Camaraarthur/daemon/WORLD_DOMINATION_STRATEGY.md

# Daemon — World Domination Strategy
*April 5, 2026 — The Machiavelli Plan*

---

## The Category We Own

**"Device-native AI"** — AI that lives on YOUR devices, not someone else's data center.

Current "personal AI" = a chatbot that remembers your name. We redefine it:
- "Can you unplug your internet and still talk to your AI? If not, it's not yours."
- "Privacy you can verify with a multimeter."
- "One AI. All your devices."

---

## The Timing Play (CRITICAL)

Every breakout project rode a wave it didn't create. Our wave: **Apple WWDC June 2026.**

Apple will announce Siri 2.0 with multi-device AI agents. When they do, every tech journalist and developer will search for "open source alternative." If Daemon v0 is live, polished, and indexed BEFORE that announcement, we're the answer. "Open-source alternative to [hot paid thing]" is the most reliable viral pattern in developer tools.

**Target: v0 public and stable by late May 2026.**

Other waves to ride:
- EU AI Act high-risk obligations (August 2026) → "Daemon is compliant by design"
- Any major AI privacy scandal → "Privacy you can verify with a multimeter"
- Any Replika/Character.ai shutdown → "Your daemon can't be taken away"

---

## Phase 0: Before Launch (NOW → v0 public)

### IP Protection (do before ANYTHING goes public)
- [x] EUIPO SME Fund voucher submitted
- [ ] File Italian patent for privacy LED interlock (~€300)
- [ ] File "DAEMON" trademark at EUIPO when voucher approved (~€225 after reimbursement)
- [ ] CRITICAL: Patent must be filed BEFORE GitHub repo goes public

### Free Cloud Credits (15 min each)
- [ ] NVIDIA Inception
- [ ] Microsoft for Startups ($150K Azure)
- [ ] AWS Activate ($100-300K)

### Build the Ammo
- [ ] Film the multimeter video (60 sec, measure LED interlock pin)
- [ ] Record split-screen demo: ChatGPT vs Daemon (same prompt, Daemon knows you)
- [ ] Record "all devices connected" 30-sec clip (phone + laptop + RPi, one conversation)
- [ ] Prepare 3 blog posts (see Content Pipeline below)
- [ ] Print 500 stickers: "Privacy you can verify with a multimeter" + QR → daemon.page

### Community Infrastructure
- [ ] GitHub Discussions enabled (NOT Discord yet — 5 people in Discord is a ghost town)
- [ ] 15 "good first issue" labels with clear descriptions
- [ ] CONTRIBUTING.md that gets someone running in <5 minutes
- [ ] username.daemon.page working (every user = an ad)

---

## Phase 1: Launch Week (v0 goes public)

### Day 0: Show HN
- **Post:** `Show HN: Daemon – Open-source AI agent that connects all your devices`
- **Time:** Tuesday or Wednesday, 9 AM ET (2 PM CET)
- **Requirements:** Working demo anyone can try in <2 minutes, clean README, honest about limitations
- **Arthur camps in comments for 3+ hours answering everything**

### Day 0-1: Reddit Wave (staggered)
- **r/LocalLLaMA** (same day as HN, afternoon) — Frame: "I built a multi-device AI agent with BYOK. Supports local models."
- **r/selfhosted** (Day 1) — Frame: "Self-hosted AI agent with zero cloud dependency. Your data stays on your devices."
- **r/SideProject** (Day 2) — Frame: build story, solo founder, Turin, Arduino heritage

### Day 0: Newsletter Submissions
Submit to all simultaneously:
- Console.dev (PERFECT fit — they review CLI tools)
- TLDR AI
- The Rundown AI
- Changelog News
- AlphaSignal
- Ben's Bites (email directly)

### Day 1-3: Twitter/X
- Post the multimeter video
- Post the split-screen demo
- Tag/quote-tweet relevant accounts (see Target List)
- Start the build-in-public thread

### Day 3-7: YouTube Outreach
DM these creators with a concise pitch (3 sentences + demo link + GitHub):
- **Cole Medin** — Reviews smaller AI agent tools specifically
- **Matthew Berman** — Reviews AI tools, responsive to DMs
- **Dreams of Code** — CLI tool focused
- **All About AI** — Hands-on demos of smaller projects
- **NetworkChuck** — Self-hosted angle

### Day 7: Podcast Pitches
- devtools.fm (specifically about developer tools)
- Changelog / The Changelog (THE open-source podcast)
- Latent Space (DM swyx on Twitter)
- Software Engineering Daily
- Indie Hackers Podcast

---

## Phase 2: First 100 Users (Weeks 2-6)

### Turin IRL — "Collison Installation"
Get 10 loyal users by physically installing Daemon on their devices:

1. **Talk at Politecnico di Torino** — Contact DAUIN department, offer guest lecture on "Multi-device AI agents." Bring the PCB. Let students hold it.
2. **Toolbox Coworking lightning talk** — 15-min demo, split-screen, let people try it live
3. **Weekly "Daemon Office Hours"** — Thursday 6PM, Toolbox or a coffee shop. "Bring your laptop, I'll set up your daemon." This is the Stripe "Collison Installation" playbook.
4. **Arduino community crossover** — Post in Arduino forums. "Built in Turin, where Arduino was born."
5. **GDG Torino / Linux Day** — Open-source + AI talk

### Sticker Campaign
- 500 stickers, two designs: (a) Daemon logo, (b) "My AI runs locally" + QR code
- Distribute at: Toolbox, Politecnico library, TAG, coffee shops near university
- Cost: ~€40. Impact: laptops → conferences → years of impressions

### Content Pipeline (weekly)
| Week | Content | Platform |
|---|---|---|
| 1 | "I designed a 160-component PCB to make AI trustworthy" | HN, blog |
| 2 | KiCad PCB layout time-lapse | Twitter/X, YouTube |
| 3 | "The LED that can't lie" — privacy interlock deep dive | HN, blog |
| 4 | "My first 3 PCB designs failed" — failure content | Twitter/X, Reddit |
| 5 | BOM breakdown — every component and its cost | Reddit r/electronics, blog |
| 6 | "What happens when the internet goes down" — offline test video | Twitter/X, YouTube |

### Engage (don't promote) in These Communities
- **Latent Space Discord** — swyx's community, AI engineers
- **LocalLLaMA Discord** — Local AI enthusiasts
- **Ollama Discord** — BYOK angle
- **Anthropic Discord** — Claude users
- Spend 2 weeks being helpful BEFORE mentioning Daemon

---

## Phase 3: 100 → 1,000 Users (Months 2-4)

### Viral Mechanics (built into the product)
- **username.daemon.page** — Every deploy is an ad (Vercel model)
- **"Daemon Connected" status cards** — Shareable: "3 devices, 47 days uptime, 100% local"
- **Daemon fingerprint** — Unique visual per instance (like GitHub identicons). People screenshot and share.
- **CLI easter egg** — 1 in 50 commands: "Enjoying Daemon? ⭐ github.com/..."
- **"Works with Daemon" badge** — Other projects put it in their README
- **Referral unlock** — "Invite 3 friends, unlock multi-model routing"

### Content Creators (Tier 2 — after traction)
Reach out when you have 500+ stars:
- **Fireship** — Watches HN/Twitter trends, will find you if you trend
- **Theo (t3.gg)** — Very opinionated, covers indie tools
- **The Primeagen** — Reacts to trending dev content
- **sentdex** — Python/AI, covers open-source

### Press Outreach
When you have 1,000+ stars and a working hardware prototype:

| Publication | Angle |
|---|---|
| **Hackaday** | The PCB, the LED interlock, the build. tips@hackaday.com |
| **Ars Technica** | Privacy architecture, local-first AI |
| **The Verge** | "This guy built his own Apple Intelligence" |
| **Wired Italy** | Turin founder, Arduino heritage, Italian innovation |
| **404 Media** | Hardware privacy verification, surveillance resistance |
| **The Register** | "Bloke in Turin builds AI pendant with a soldering iron" |
| **Tom's Hardware** | The pendant, the PCB design |
| **Il Sole 24 Ore / Nova** | Italian startup, local success story |

**Pitch template (3 sentences):**
> "I'm building Daemon, an open-source AI that runs on your own devices with a custom 160-component hardware pendant. Unlike cloud AI, the microphone has a hardware interlock you can verify with a multimeter — no software can override it. Launching [date], want an early look? [link]"

---

## Phase 4: Kickstarter (Months 4-6)

### Prerequisites
- [ ] 2,500+ email signups (20-40% convert to backers)
- [ ] Working hardware prototype (not just renders)
- [ ] Professional renders + real photos (need both)
- [ ] 2-3 minute video: Problem (30s) → Demo (60s) → Why you (30s) → Ask (15s)
- [ ] 500+ GitHub stars as social proof

### Launch Strategy
- Set funding goal LOW (need €50K? Set goal at €15K → "funded in 48 hours" story)
- Early backer reward: username.daemon.page (viral mechanic as reward)
- Stretch goals planned in advance (each = news hook + excuse to email list)
- Pre-launch page on Kickstarter 7 days before (followers get notified)

### Kickstarter Narrative
- "Your daemon already exists as software. Now give it a body."
- "Built in Turin, where Arduino was born. Open source down to the circuit board."
- "The AI device with privacy you can measure, not just promise."

---

## Phase 5: Amazon Store + Ecosystem (Month 3+)

### "Daemon-Compatible Devices" Page
Create a page on daemon.page with affiliate links:
- Single-board computers (Raspberry Pi 5, Orange Pi)
- USB microphones, cameras, sensors
- Smart home bridges (Zigbee/Z-Wave USB dongles)
- Storage for local AI models
- Networking (Tailscale-compatible hardware)
- "Daemon Starter Kit" — curated everything-you-need list

### Revenue: Primarily Marketing
~€75/month in affiliate revenue, but the real value:
- Makes Daemon feel like a platform/ecosystem
- Content hooks ("I tested 5 USB mics for local AI — here's the best")
- Traffic from Amazon search → daemon.page

---

## Target People (The Hit List)

### Twitter/X — The Kingmakers
| Handle | Who | Why |
|---|---|---|
| @simonw | Simon Willison | #1 target. CLI tools, open source, AI, privacy, SQLite. If he blogs about you, you're legitimized. |
| @levelsio | Pieter Levels | Indie hacker godfather. Loves solo founders building in public. |
| @swyx | Shawn Wang | "AI Engineer" movement. Runs AI Engineer Summit. |
| @karpathy | Andrej Karpathy | Seismic when he covers tools (rare). |

### YouTube — Drive GitHub Stars
| Creator | Subs | Why |
|---|---|---|
| Cole Medin | 100K+ | Reviews smaller AI agent tools, very accessible |
| Matthew Berman | 400K | AI tool reviews, responsive to DMs |
| Dreams of Code | 200K | CLI/terminal tool focused |
| NetworkChuck | 4M | Self-hosted, CLI, AI |
| Jeff Geerling | 1M+ | Hardware + self-hosted. Perfect for hardware phase. |

### Podcasts
| Show | Access |
|---|---|
| devtools.fm | DM on Twitter |
| The Changelog | Submit via changelog.com |
| Latent Space | DM swyx |
| Indie Hackers | Apply on site |

---

## The Turin Advantage

**Arduino was born in Turin.** Use this:
- "Daemon is built in Turin, where Arduino was born. Hardware-first open source is in our DNA."
- Politecnico di Torino = recruiting ground (34K students, strong CS/EE)
- I3P incubator = instant credibility
- Toolbox Coworking = home base + events
- CIM4.0 (Turin EDIH) = free AI services for Piemonte SMEs

---

## Budget

| Item | Cost | When |
|---|---|---|
| 500 stickers | €40 | Now |
| Italian patent filing | €300 (€100 after SME Fund) | This month |
| DAEMON trademark | €900 (€225 after SME Fund) | When voucher approved |
| Domain/hosting | €50-200/month | Already running |
| Everything else | €0 | Sweat equity |

**Total cash needed to launch: ~€500**

Everything else is time, creativity, and relentless execution.

---

## The One Rule

**Ship, then optimize.** The product must work flawlessly for 10 people before marketing to 10,000. Every bug a creator encounters on camera is a permanent scar. Every delightful first experience is a permanent evangelist.

The strategy is:
1. Get 10 local users who love it
2. Film them using it
3. Use that footage to get 100
4. Use those 100 to get 1,000
5. Use those 1,000 for Kickstarter
6. Use Kickstarter for press
7. Use press for scale

No step can be skipped. No step is optional.
