Camaraarthur/daemon/docs/positioning.md

# Daemon — Positioning v1

> **Status:** locked.
> **Date:** 2026-04-08
> **Pair with:** vision.md (the WHAT). This doc is the PITCH.

## 1. The wedge — sharper than before

### v1 audience: Claude Code power users (developers)

**Why this audience first:**
- Highest acute pain (already daily users hitting "my agent died when I closed my laptop")
- Lowest CAC: ~5 places to reach them (Anthropic Discord, /r/ClaudeAI, HN, /r/LocalLLaMA, a few Twitter circles)
- Strongest demos (devs film themselves; dev demos go viral)
- They overlap with privacy-conscious people, homelabbers, hardware tinkerers — picking devs gets the others for free
- AGPLv3 actually matters here (only audience that reads licenses)
- Reference customers ARE the artifact (a daemon-built workflow on GitHub is worth 10× a testimonial)

**Why NOT the casual prosumer first:**
- They expect a website, not a daemon process
- They need a trust brand we don't have yet
- Conversion path needs polished onboarding + hand-holding
- Won't pay until they see other people happy first

**Why NOT homelab first either:**
- They want fun, not relief
- Lower density than Claude Code communities
- They overlap with devs anyway — devs is a strict superset

### v1.5 audience: privacy-first knowledge workers + homelabbers

Natural extension of v1. Privacy is the closer for v1 devs, the opener for v1.5 audiences.

### v2 audience: casual prosumers

After the wedge produces organic word of mouth.

## 2. The two seductions

The dev pitch and the casual pitch are *different surfaces of the same product*. They share the same install, same protocol, same architecture — but the framing is different.

### Dev seduction (v1 — lead with this)

> Your Claude Code, on every device you own.

You already live in Claude Code. But your agent dies when you close the lid, forgets when you switch machines, and can't touch your phone. Daemon gives Claude Code a persistent memory, a web UI, and a tool bus that reaches every device you own — laptop, desktop, phone, daemon-key — as one continuous session. Bring your own Anthropic key. Your data never touches our servers.

### Casual seduction (v1.5)

> An AI that searches your computer, runs in the background, and pings you when it's done.

Drop the pendant on your desk. Pair it with your phone. Now an AI agent runs while you sleep — checks your email, watches your sensors, runs jobs, builds you tools. Ask it from your phone to find that file you saved last Tuesday. It does. No upload, no chat-bot UI for the simple stuff. Just a thing that works on your real life.

The bridge between them: the vibe coder's primitive set is the same. The dev uses it to build personal automations on top of their existing Claude Code workflow. The casual user gets pre-built primitives (morning briefing, find-my-file, build-me-a-tool) that come out of the box.

## 3. The "so what" — locked

**One sentence:**
> Daemon is the AI agent that runs on your stuff, not in someone's cloud.

**Hero paragraph:**
> Daemon runs a small agent on every device you own — laptop, desktop, phone, the always-on box on your desk. They join one continuous AI agent that has access to your files, your sensors, your shell, your screen. Your conversations and memory live on those devices, never on our servers. Bring your own model API key. Open source, self-hostable, AGPLv3. The same agent, the same memory, on everything you actually use.

**30-second verbal pitch (memorize, end with URL not a question):**
> "You know Claude Code — the terminal thing? I use it every day but it dies when I close my laptop and it can't touch my phone. So I built daemon — same agent, same memory, but it runs as a tiny process on every device I own. I can ask it from my phone to grep a file on my desktop and it just does it. My data never hits a server, the relay only routes messages. Open source, works with any model. It's at daemon.page."

**The pitch is true.** Anchored in the actual technology (per-device daemon, persistent memory, BYOK relay). Legible to a non-technical person ("ask my phone to do something on my laptop"). Picks a category — "Claude Code" — that everyone in the wedge already knows. **Cursor won by being "VSCode + AI." Daemon wins by being "Claude Code + multi-device."**

## 4. Strategic NO list (don't say these in v1)

- **Don't lead with "AI agent."** Crowded category, you lose on polish.
- **Don't lead with "privacy" or "AGPLv3."** Privacy is the closer, not the opener. Signals "not for serious work" to devs even though it's true.
- **Don't mention the daemon-key Pi.** Sounds like a Kickstarter, not a product. Park it.
- **Don't say "personal AI."** Rabbit / Humane / Friend poisoned that brand.
- **Don't say "memory for agents."** That's Letta's lane and it describes mechanism, not pain.
- **Don't show a chat window as the primary screenshot.** Show "phone running command on laptop." That's the unique demo.
- **Don't compete on model quality.** BYOK = model-agnostic, don't get drawn into "smarter than GPT-5."
- **Don't use the word "daemon" in the tagline without context.** Half the audience hears the technical term, the other half hears the demon.
- **Don't sell to enterprises in v1.** Long sales cycles, kills the flywheel.
- **Don't add Telegram integration in v1.** Notifications are owned natively.
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
