Camaraarthur/daemon/test-results/20260405-204737/after_delay.png

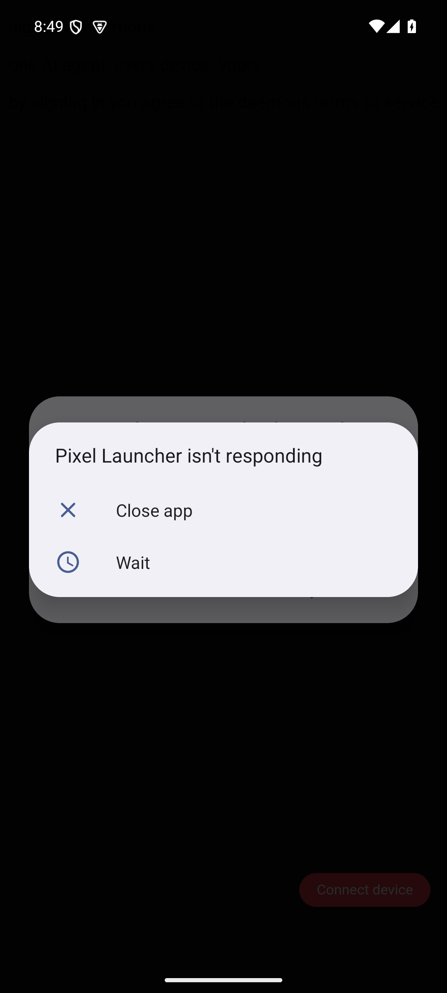
test-results/20260405-204737/after_delay.png
