Camaraarthur/daemon/server/esp32_firmware/font5x7.py

# 5x7 bitmap font for MicroPython ST7789 display
# Each character is 5 columns of 7-bit rows, packed as bytes
# Covers ASCII 32-126

FONT = {
    32: b'\x00\x00\x00\x00\x00',  # space
    33: b'\x00\x00\x5f\x00\x00',  # !
    34: b'\x00\x07\x00\x07\x00',  # "
    39: b'\x00\x00\x07\x00\x00',  # '
    40: b'\x00\x1c\x22\x41\x00',  # (
    41: b'\x00\x41\x22\x1c\x00',  # )
    42: b'\x14\x08\x3e\x08\x14',  # *
    43: b'\x08\x08\x3e\x08\x08',  # +
    44: b'\x00\x50\x30\x00\x00',  # ,
    45: b'\x08\x08\x08\x08\x08',  # -
    46: b'\x00\x60\x60\x00\x00',  # .
    47: b'\x20\x10\x08\x04\x02',  # /
    48: b'\x3e\x51\x49\x45\x3e',  # 0
    49: b'\x00\x42\x7f\x40\x00',  # 1
    50: b'\x42\x61\x51\x49\x46',  # 2
    51: b'\x21\x41\x45\x4b\x31',  # 3
    52: b'\x18\x14\x12\x7f\x10',  # 4
    53: b'\x27\x45\x45\x45\x39',  # 5
    54: b'\x3c\x4a\x49\x49\x30',  # 6
    55: b'\x01\x71\x09\x05\x03',  # 7
    56: b'\x36\x49\x49\x49\x36',  # 8
    57: b'\x06\x49\x49\x29\x1e',  # 9
    58: b'\x00\x36\x36\x00\x00',  # :
    63: b'\x02\x01\x51\x09\x06',  # ?
    65: b'\x7e\x11\x11\x11\x7e',  # A
    66: b'\x7f\x49\x49\x49\x36',  # B
    67: b'\x3e\x41\x41\x41\x22',  # C
    68: b'\x7f\x41\x41\x22\x1c',  # D
    69: b'\x7f\x49\x49\x49\x41',  # E
    70: b'\x7f\x09\x09\x09\x01',  # F
    71: b'\x3e\x41\x49\x49\x7a',  # G
    72: b'\x7f\x08\x08\x08\x7f',  # H
    73: b'\x00\x41\x7f\x41\x00',  # I
    74: b'\x20\x40\x41\x3f\x01',  # J
    75: b'\x7f\x08\x14\x22\x41',  # K
    76: b'\x7f\x40\x40\x40\x40',  # L
    77: b'\x7f\x02\x0c\x02\x7f',  # M
    78: b'\x7f\x04\x08\x10\x7f',  # N
    79: b'\x3e\x41\x41\x41\x3e',  # O
    80: b'\x7f\x09\x09\x09\x06',  # P
    81: b'\x3e\x41\x51\x21\x5e',  # Q
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
}

def char_width():
    return 6  # 5px + 1px spacing

def char_height():
    return 8  # 7px + 1px spacing
