Camaraarthur/daemon/server/tools_mcp.py

#!/usr/bin/env python3
"""
MCP Server — Custom tools for the daemon.
Provides SSH, device listing, sensor reading, audio, and display tools.
Runs as a stdio MCP server, loaded by Claude Code via --mcp-config.
"""

import asyncio
import json
import subprocess
import sys
import time
from typing import Any

# Simple MCP stdio server implementation
# Protocol: JSON-RPC 2.0 over stdin/stdout


TOOLS_PHONE = {
    "name": "phone_command",
    "description": "Send a command to a connected Android phone via the daemon app. The phone runs a background service that can: take_photo, get_location, read_sensors, get_battery, get_device_info, send_notification, list_files, read_file, bluetooth_scan. Returns JSON result.",
    "inputSchema": {
        "type": "object",
        "properties": {
            "command": {
                "type": "string",
                "description": "Command type: take_photo, get_location, read_sensors, get_battery, get_device_info, send_notification, list_files, read_file",
                "enum": ["take_photo", "get_location", "read_sensors", "get_battery", "get_device_info", "send_notification", "list_files", "read_file"],
            },
            "params": {
                "type": "object",
                "description": "Optional parameters (e.g. {\"path\": \"/storage/emulated/0/DCIM\"} for list_files, {\"title\": \"hello\", \"body\": \"world\"} for send_notification)",
            },
            "device_id": {
                "type": "string",
                "description": "Device ID (default: Pixel 8 Pro)",
                "default": "Pixel 8 Pro",
            },
        },
        "required": ["command"],
    },
}

TOOLS_ESP32 = {
    "name": "esp32_command",
    "description": "Send a MicroPython command to the ESP32 daemon key over WiFi via the phone. The ESP32 has a ST7789 display (240x280) and distance sensor. Display: tft.fill(0), tft.text(font, 'text', x, y, color), tft.fill_rect(x, y, w, h, color). Colors: st7789.RED, st7789.WHITE, st7789.BLACK. Sensor: read_distance() returns cm. Goes through phone's WiFi TCP to ESP32 REPL on port 8266.",
    "inputSchema": {
        "type": "object",
        "properties": {
            "command": {
                "type": "string",
                "description": "MicroPython command to execute on the ESP32 REPL",
            },
        },
        "required": ["command"],
    },
}

TOOL_PLOT_WEB = {
    "name": "plot_sensor_web",
    "description": "Start or stop streaming live ESP32 sensor data to the daemon's public web page (my.daemon.page). The canvas will automatically appear/disappear. Actions: 'start' begins plotting distance sensor every 2s, 'stop' hides the canvas, 'once' does a single read and push.",
    "inputSchema": {
        "type": "object",
        "properties": {
            "action": {
                "type": "string",
                "description": "start, stop, or once",
                "enum": ["start", "stop", "once"],
            },
        },
        "required": ["action"],
    },
}

TOOL_PLOT_ESP32 = {
    "name": "plot_sensor_esp32",
    "description": "Display live sensor data on the ESP32's screen in a nice red graph/number display. Actions: 'start' begins updating the display with distance readings, 'stop' clears the display, 'once' shows current reading.",
    "inputSchema": {
        "type": "object",
        "properties": {
            "action": {
                "type": "string",
                "description": "start, stop, or once",
                "enum": ["start", "stop", "once"],
            },
        },
        "required": ["action"],
    },
}

TOOL_PUSH_WEB = {
    "name": "push_to_web",
    "description": "Push arbitrary content to the daemon's public web page canvas. Can push text, sensor data, or clear the canvas.",
    "inputSchema": {
        "type": "object",
        "properties": {
            "type": {
                "type": "string",
                "description": "Content type: 'text', 'sensor', or 'clear'",
                "enum": ["text", "sensor", "clear"],
            },
            "text": {
                "type": "string",
                "description": "Text to display (for type=text)",
            },
            "distance": {
                "type": "number",
                "description": "Distance value in cm (for type=sensor)",
            },
        },
        "required": ["type"],
    },
}

TOOLS = [
    {
        "name": "ssh_run",
        "description": "Run a command on a remote device via SSH. Available devices: arturito (Linux server), msi (Windows laptop), pixel (Android/Termux). Returns stdout+stderr.",
        "inputSchema": {
            "type": "object",
            "properties": {
                "host": {
                    "type": "string",
                    "description": "SSH host alias: 'arturito', 'msi', or 'pixel'",
                    "enum": ["arturito", "msi", "pixel"],
                },
                "command": {
                    "type": "string",
                    "description": "Command to execute on the remote device",
                },
                "timeout": {
                    "type": "integer",
                    "description": "Timeout in seconds (default 30)",
                    "default": 30,
                },
            },
            "required": ["host", "command"],
        },
    },
    {
        "name": "list_devices",
        "description": "List all known devices in the Tailscale mesh with their status (online/offline).",
        "inputSchema": {
            "type": "object",
            "properties": {},
        },
    },
    {
        "name": "device_info",
        "description": "Get detailed info about a specific device: OS, uptime, disk, memory, network.",
        "inputSchema": {
            "type": "object",
            "properties": {
                "host": {
                    "type": "string",
                    "description": "SSH host alias",
                    "enum": ["arturito", "msi", "pixel"],
                },
            },
            "required": ["host"],
        },
    },
    {
        "name": "list_usb_devices",
        "description": "List USB devices connected to a host.",
        "inputSchema": {
            "type": "object",
            "properties": {
                "host": {
                    "type": "string",
                    "description": "SSH host alias (default: local machine)",
                    "default": "arturito",
                },
            },
        },
    },
    TOOLS_PHONE,
    TOOLS_ESP32,
    TOOL_PLOT_WEB,
    TOOL_PLOT_ESP32,
    TOOL_PUSH_WEB,
    {
        "name": "scan_i2c",
        "description": "Scan I2C bus for connected sensors. Returns detected addresses and likely device types.",
        "inputSchema": {
            "type": "object",
            "properties": {
                "host": {
                    "type": "string",
                    "description": "SSH host alias where I2C devices are connected",
                    "default": "arturito",
                },
                "bus": {
                    "type": "integer",
                    "description": "I2C bus number (default 1 for Raspberry Pi)",
                    "default": 1,
                },
            },
        },
    },
]

# Known I2C sensor addresses for auto-identification
I2C_SENSOR_DB = {
    "0x3c": "SSD1306/SSD1315 OLED Display",
    "0x3d": "SSD1306 OLED Display (alt addr)",
    "0x40": "INA219 Current Sensor / HDC1080 Humidity",
    "0x44": "SHT41/SHT45 Temp+Humidity",
    "0x48": "ADS1115 ADC / TMP102 Temperature",
    "0x50": "AT24C EEPROM",
    "0x57": "MAX30102 Heart Rate",
    "0x68": "MPU6050 IMU / DS3231 RTC",
    "0x69": "MPU6050 IMU (alt addr)",
    "0x76": "BME280/BMP280 (SDO=GND)",
    "0x77": "BME280/BMP280 (SDO=VCC) / BMP180",
}

# Device-specific info commands
DEVICE_INFO_COMMANDS = {
    "arturito": "echo '=== OS ===' && uname -a && echo '=== Uptime ===' && uptime && echo '=== Memory ===' && free -h && echo '=== Disk ===' && df -h / && echo '=== Network ===' && hostname -I",
    "msi": 'systeminfo | findstr /B /C:"OS Name" /C:"OS Version" /C:"System Manufacturer" /C:"Total Physical Memory" && echo === Uptime === && net stats workstation | findstr "since"',
    "pixel": "uname -a && uptime && free -h && df -h /data 2>/dev/null || df -h /",
}


def run_ssh(host: str, command: str, timeout: int = 30) -> dict:
    """Execute a command on a remote host via SSH. Local commands for arturito."""
    try:
        if host == "arturito":
            # Local execution — no SSH needed
            result = subprocess.run(
                ["bash", "-c", command],
                capture_output=True,
                text=True,
                timeout=timeout,
            )
        else:
            result = subprocess.run(
                ["ssh", host, command],
                capture_output=True,
                text=True,
                timeout=timeout,
            )
        output = result.stdout
        if result.stderr:
            output += f"\n[stderr]: {result.stderr}"
        return {"success": True, "output": output.strip(), "exit_code": result.returncode}
    except subprocess.TimeoutExpired:
        return {"success": False, "output": f"Command timed out after {timeout}s", "exit_code": -1}
    except Exception as e:
        return {"success": False, "output": str(e), "exit_code": -1}


def check_device_online(host: str) -> bool:
    """Quick check if a device is reachable via SSH."""
    try:
        result = subprocess.run(
            ["ssh", "-o", "ConnectTimeout=3", host, "echo ok"],
            capture_output=True, text=True, timeout=5,
        )
        return result.returncode == 0
    except:
        return False


async def handle_tool_call(name: str, arguments: dict) -> list[dict]:
    """Execute a tool and return MCP-formatted content."""

    if name == "phone_command":
        command = arguments["command"]
        params = arguments.get("params", {})
        device_id = arguments.get("device_id", "Pixel 8 Pro")

        # Send command to phone via WebSocket server HTTP API
        import urllib.request
        import json as json_mod

        request_id = f"req-{int(time.time() * 1000)}"
        payload = json_mod.dumps({
            "device_id": device_id,
            "command": {
                "type": command,
                "request_id": request_id,
                **params,
            }
        }).encode()

        try:
            # First check if device is connected
            health_req = urllib.request.Request("http://localhost:4801/health")
            health_resp = urllib.request.urlopen(health_req, timeout=3)
            health = json_mod.loads(health_resp.read().decode())
            connected_ids = [d["id"] for d in health.get("devices", []) if d.get("connected")]
            if device_id not in connected_ids:
                return [{"type": "text", "text": f"**Phone not connected.** The daemon app isn't running on {device_id}. Connected devices: {', '.join(connected_ids) or 'none'}. Try SSH to pixel instead: ssh pixel 'command'"}]

            req = urllib.request.Request(
                "http://localhost:4801/command",
                data=payload,
                headers={"Content-Type": "application/json"},
                method="POST",
            )
            resp = urllib.request.urlopen(req, timeout=10)
            result = json_mod.loads(resp.read().decode())
            return [{"type": "text", "text": f"**Phone ({device_id}):**\n```json\n{json_mod.dumps(result, indent=2)}\n```"}]
        except Exception as e:
            return [{"type": "text", "text": f"**Phone error:** {e}\n\nIs the daemon app running on the phone? Check WebSocket: http://localhost:4801/health"}]

    elif name == "esp32_command":
        command = arguments["command"]
        # Send via phone's WebSocket → TCP to ESP32
        import urllib.request
        import json as json_mod
        try:
            payload = json_mod.dumps({
                "device_id": "Pixel 8 Pro",
                "command": {
                    "type": "esp32_command",
                    "ip": "10.27.241.196",
                    "port": 8266,
                    "command": command + "\n",
                }
            }).encode()
            req = urllib.request.Request(
                "http://localhost:4801/command",
                data=payload,
                headers={"Content-Type": "application/json"},
                method="POST",
            )
            resp = urllib.request.urlopen(req, timeout=15)
            result = json_mod.loads(resp.read().decode())
            return [{"type": "text", "text": f"**ESP32:**\n```\n{json_mod.dumps(result, indent=2)}\n```"}]
        except Exception as e:
            return [{"type": "text", "text": f"**ESP32 error:** {e}. REPL may be down — try reading via HTTP port 8268 instead."}]

    elif name == "plot_sensor_web":
        action = arguments["action"]
        import urllib.request
        import json as json_mod
        import sqlite3
        try:
            conn = sqlite3.connect("/home/arthur/daemon/data/users.db")
            token = conn.execute("SELECT token FROM sessions LIMIT 1").fetchone()[0]
            conn.close()

            if action == "start":
                # Start background streaming loop
                subprocess.Popen(
                    ["/home/arthur/daemon/server/fast_loop.sh"],
                    stdout=open("/tmp/sensor-fast.log", "w"),
                    stderr=subprocess.STDOUT,
                    env={**dict(__import__('os').environ), "HOME": "/home/arthur"},
                )
                return [{"type": "text", "text": f"**Sensor stream started** on my.daemon.page. Live distance graph updating every 2 seconds."}]
            elif action == "stop":
                # Kill the loop and clear canvas
                subprocess.run(["pkill", "-9", "-f", "fast_loop"], capture_output=True)
                subprocess.run(["pkill", "-9", "-f", "read_sensor"], capture_output=True)
                data = json_mod.dumps({"type": "clear"}).encode()
                req = urllib.request.Request(
                    "http://localhost:4800/api/stream-push", data=data,
                    headers={"Content-Type": "application/json", "Cookie": f"daemon_token={token}"},
                    method="POST")
                urllib.request.urlopen(req, timeout=3)
                return [{"type": "text", "text": f"**Sensor stream stopped.** Canvas hidden on my.daemon.page."}]
            else:
                # Single read + push
                result = subprocess.run(
                    ["/home/arthur/daemon/server/read_sensor.sh"],
                    capture_output=True, text=True, timeout=8,
                    env={**dict(__import__('os').environ), "HOME": "/home/arthur"})
                dist = float(result.stdout.strip())
                data = json_mod.dumps({"type": "sensor", "distance": dist, "timestamp": int(time.time()*1000)}).encode()
                req = urllib.request.Request(
                    "http://localhost:4800/api/stream-push", data=data,
                    headers={"Content-Type": "application/json", "Cookie": f"daemon_token={token}"},
                    method="POST")
                urllib.request.urlopen(req, timeout=3)
                return [{"type": "text", "text": f"**Single read:** {dist:.1f} cm pushed to web."}]
        except Exception as e:
            return [{"type": "text", "text": f"**Stream error:** {e}"}]
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
